merstoffe14/WP_Plantjes/images/280670132_730538967991783_6660131392470541068_n.jpg

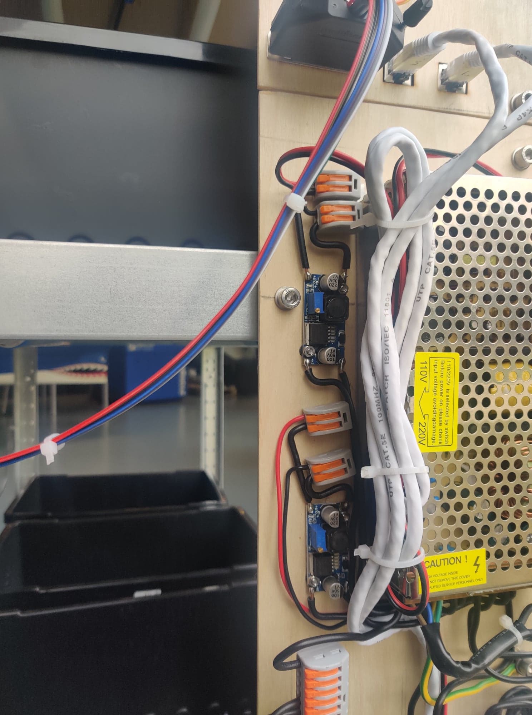
images/280670132_730538967991783_6660131392470541068_n.jpg
